shurik179/povstaff/docs/images/kit-bagA.jpg

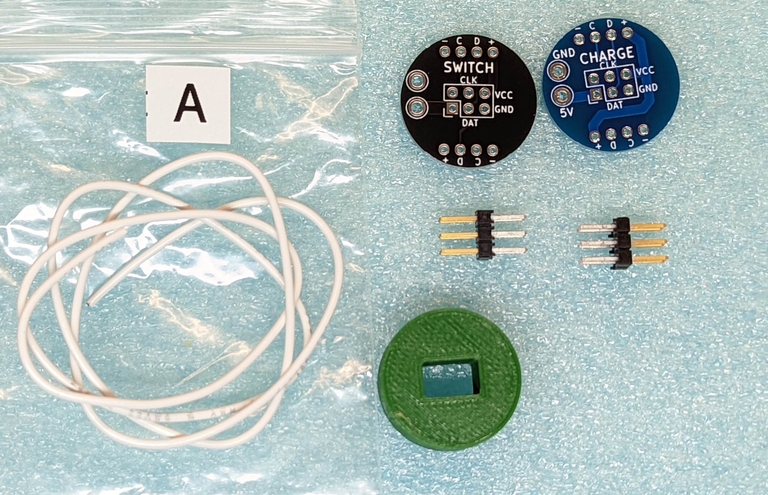
docs/images/kit-bagA.jpg
