shurik179/povstaff/docs/images/kit-bagB.jpg

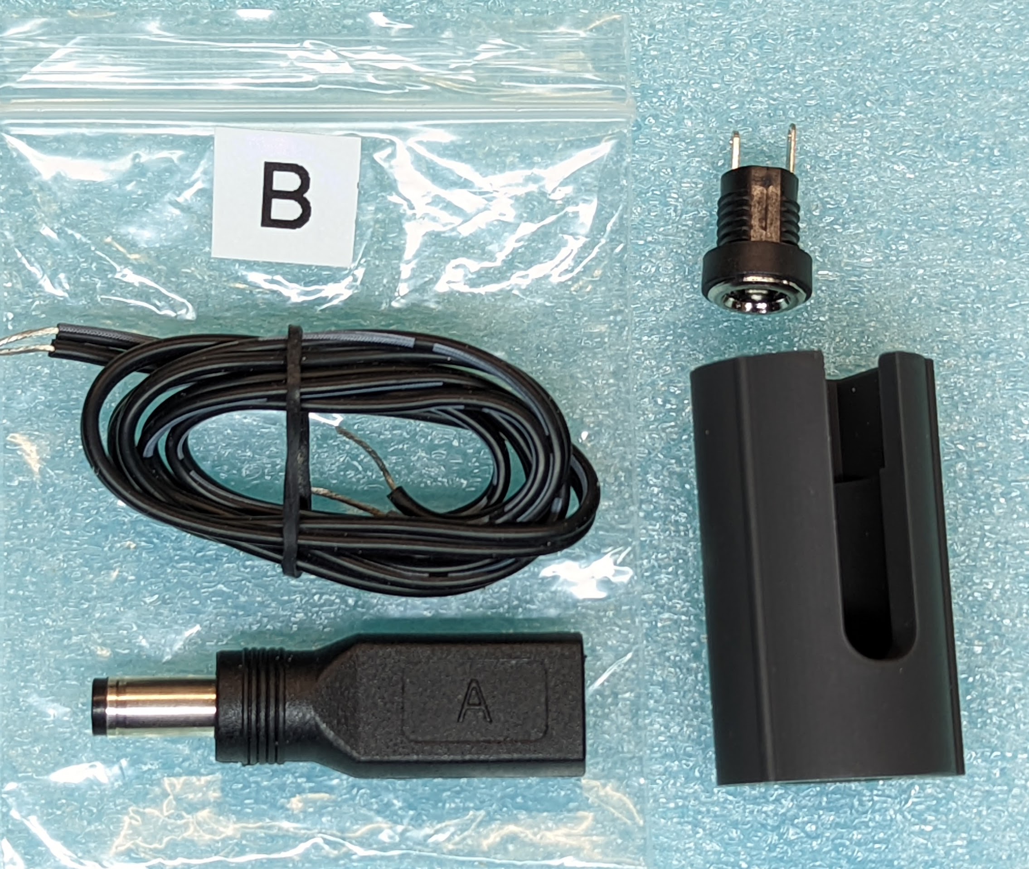
docs/images/kit-bagB.jpg
