shurik179/povstaff/docs/images/kit-bagC.jpg

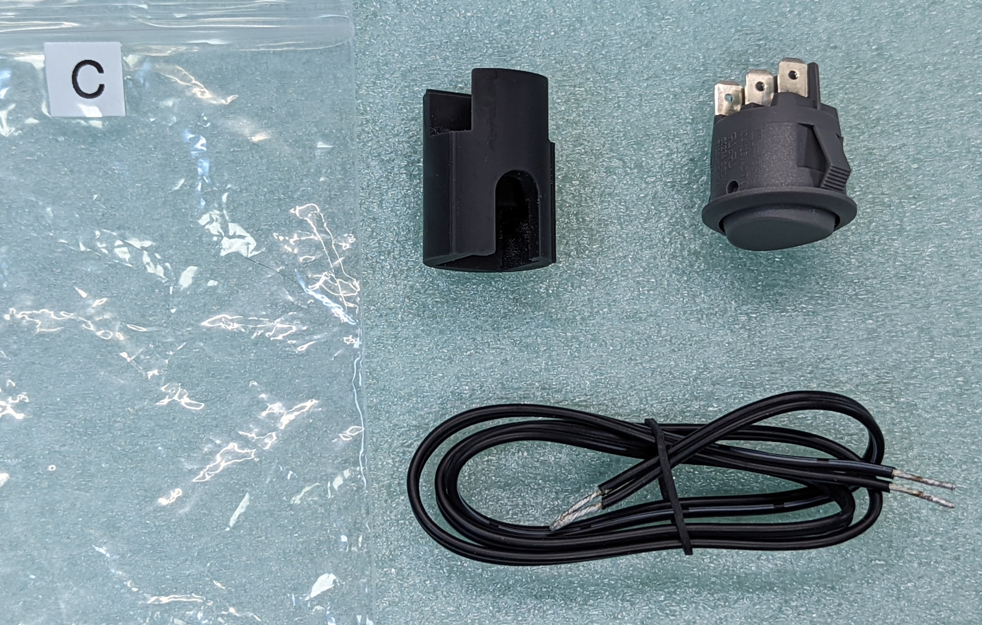
docs/images/kit-bagC.jpg
