shurik179/povstaff/docs/images/kit-bagD.jpg

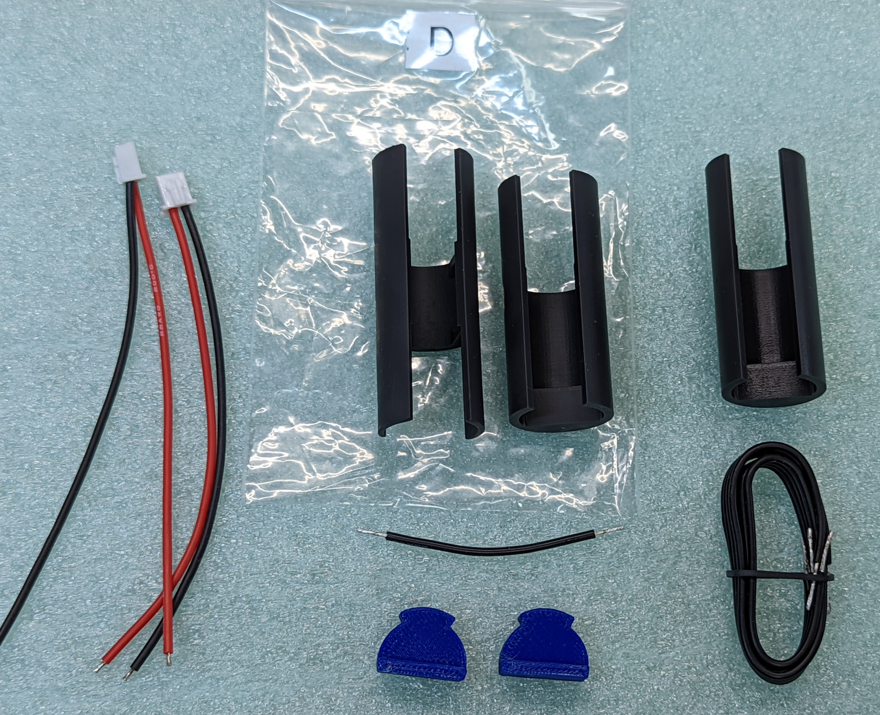
docs/images/kit-bagD.jpg
