shurik179/povstaff/docs/images/kit-bagE.jpg

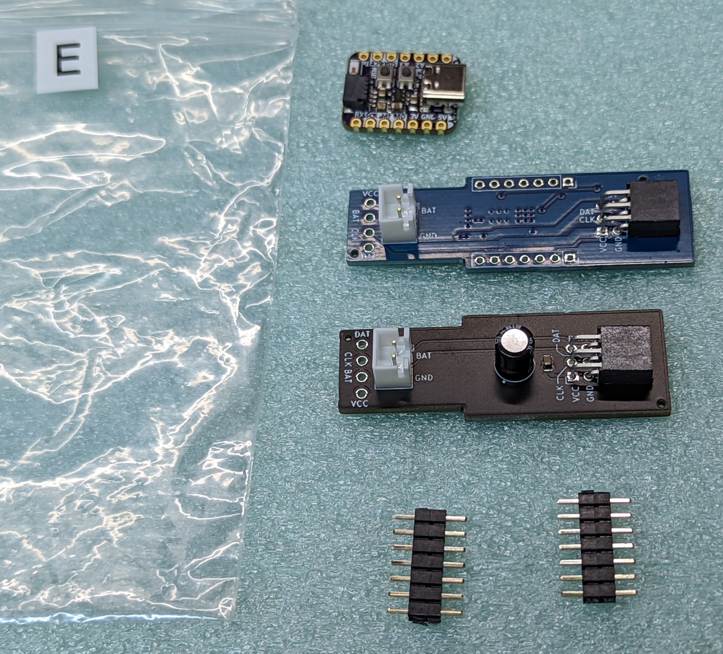
docs/images/kit-bagE.jpg
