shurik179/povstaff/docs/images/kit-bagF.jpg

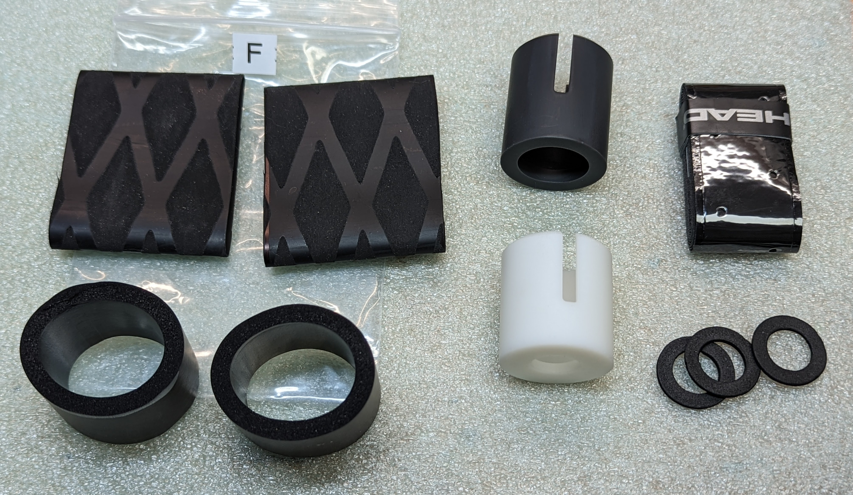
docs/images/kit-bagF.jpg
