shurik179/povstaff/docs/images/kit-switch.jpg

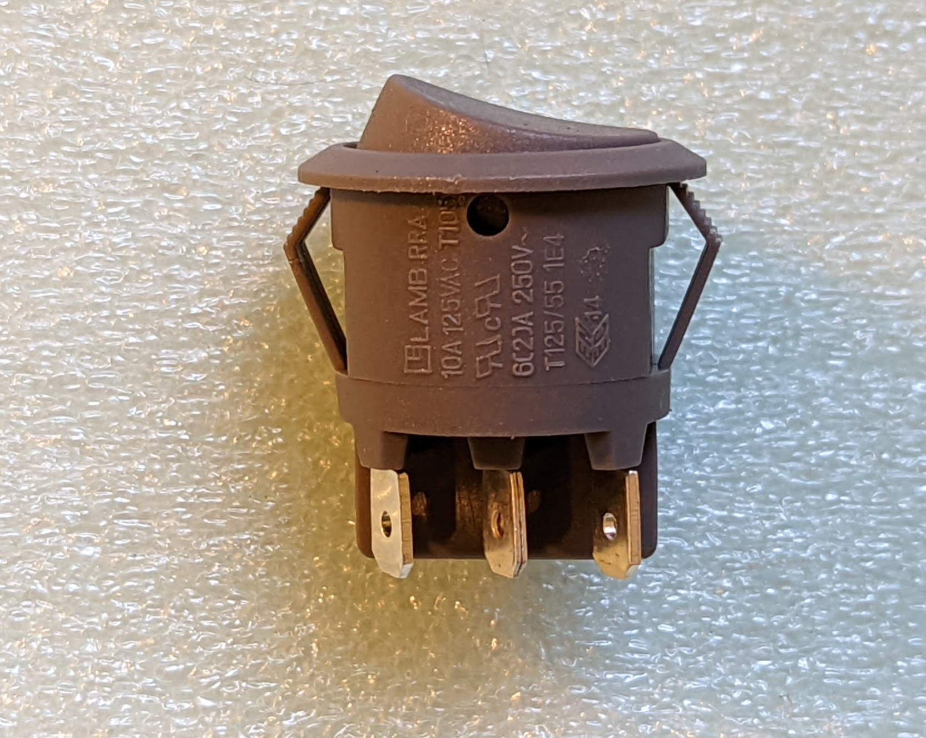
docs/images/kit-switch.jpg
