shurik179/povstaff/docs/images/main.jpg

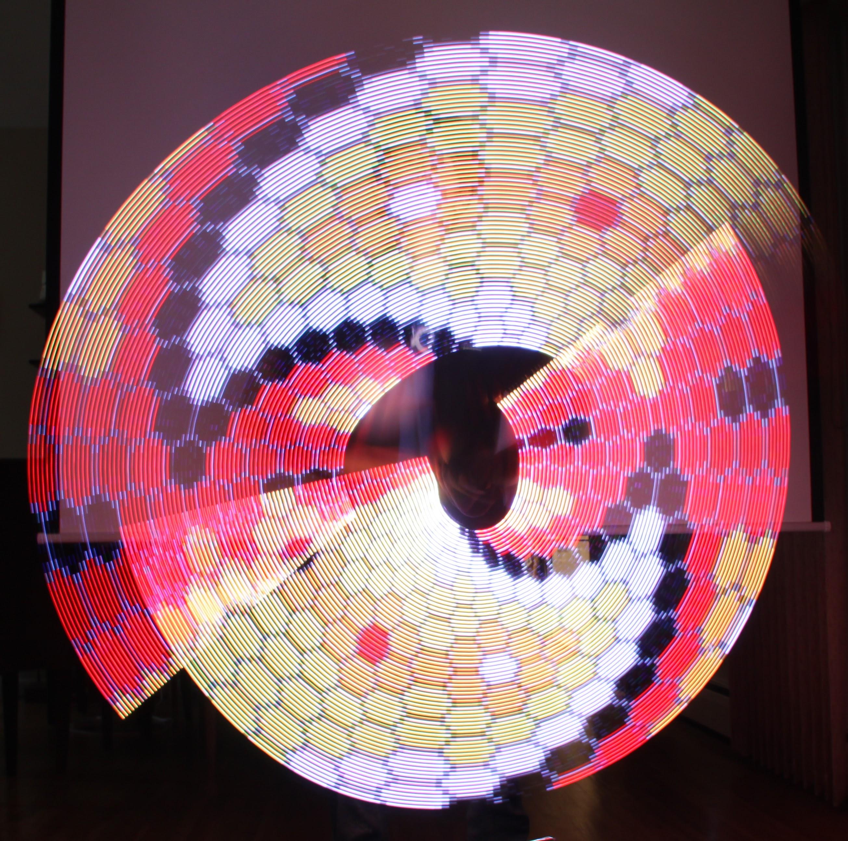
docs/images/main.jpg
