shurik179/povstaff/docs/images/PDB-5.jpg

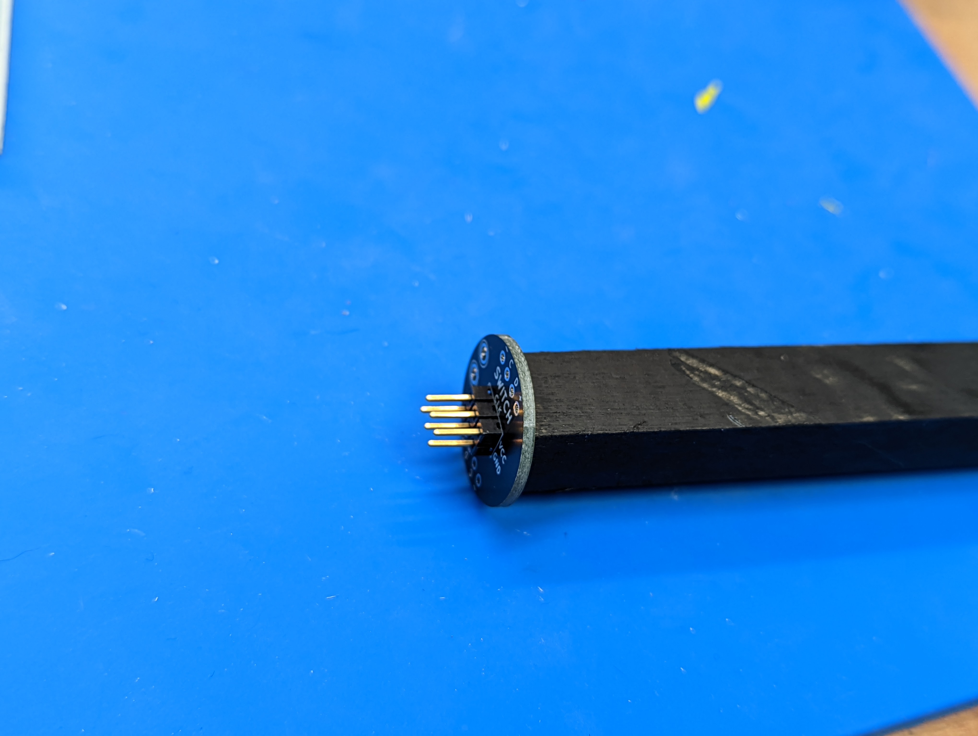
docs/images/PDB-5.jpg
