shurik179/povstaff/docs/images/PXL_20230427_031914252.jpg

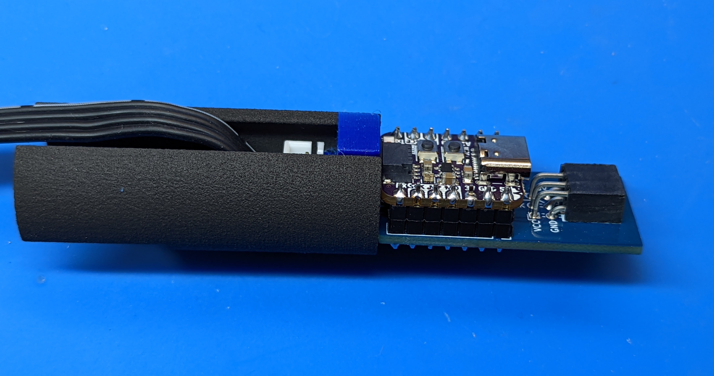
docs/images/PXL_20230427_031914252.jpg
