shurik179/povstaff/docs/images/unsorted-March30/controller-9.jpg

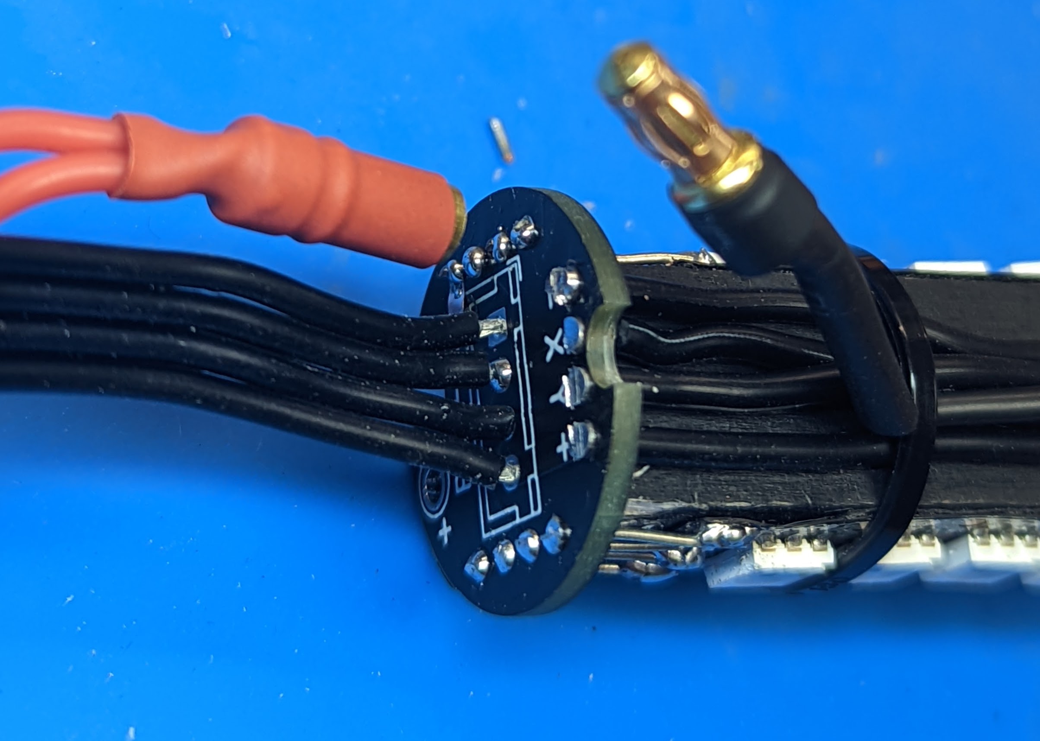
docs/images/unsorted-March30/controller-9.jpg
